spectricarus/EGL314_TeamF/Final/Software/assets/backgrounds/#1.png

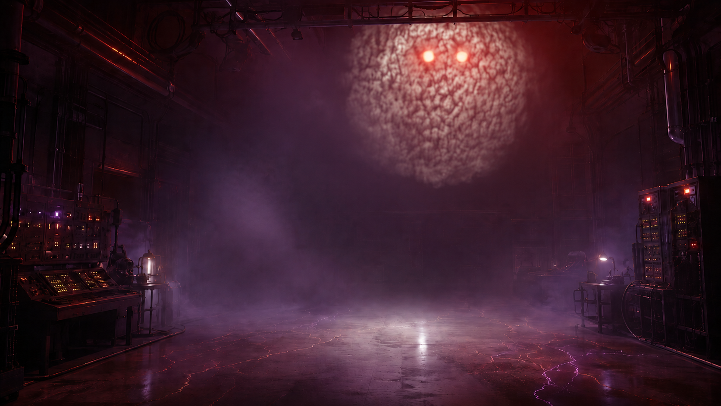
Final/Software/assets/backgrounds/#1.png
