spectricarus/EGL314_TeamF/Final/Software/assets/backgrounds/#3.png

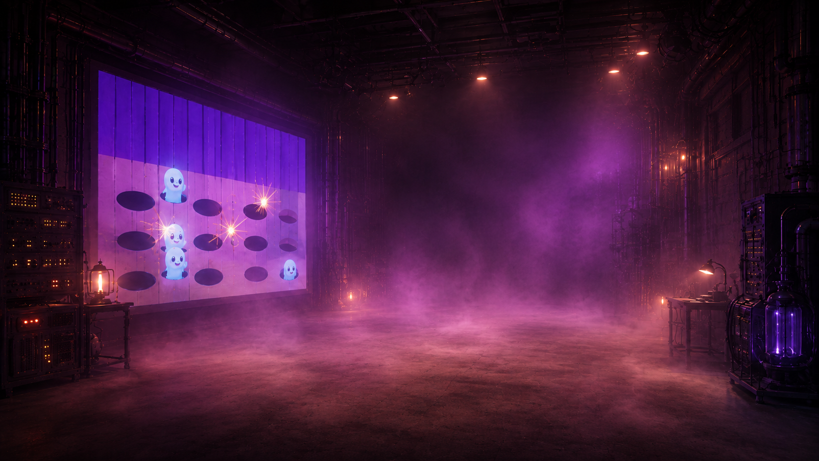
Final/Software/assets/backgrounds/#3.png
