spectricarus/EGL314_TeamF/Final/Software/assets/backgrounds/#5.png

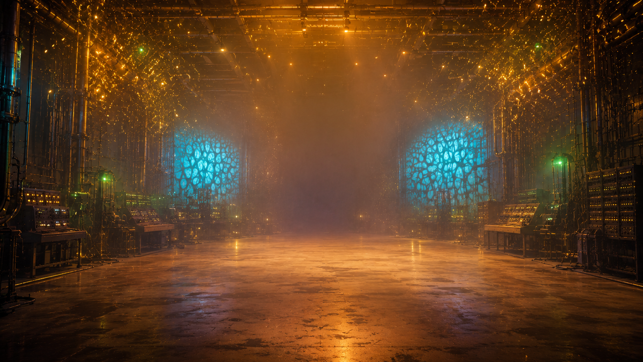
Final/Software/assets/backgrounds/#5.png
