spectricarus/EGL314_TeamF/MVP/Software/assets/pipeline-diagram.png

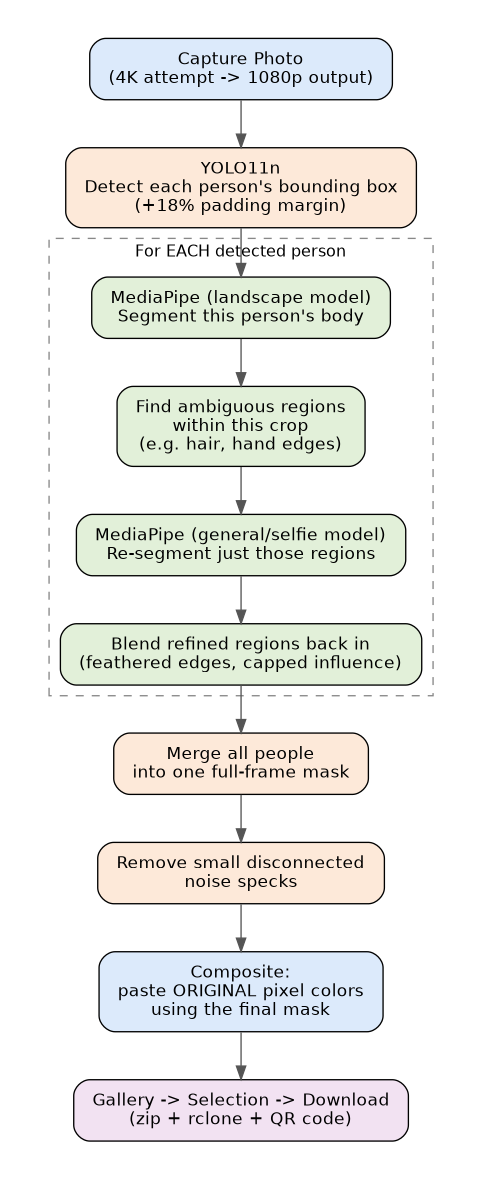
MVP/Software/assets/pipeline-diagram.png
