spectricarus/EGL314_TeamF/POC/images/power_touchcreen_via_pi.jpg

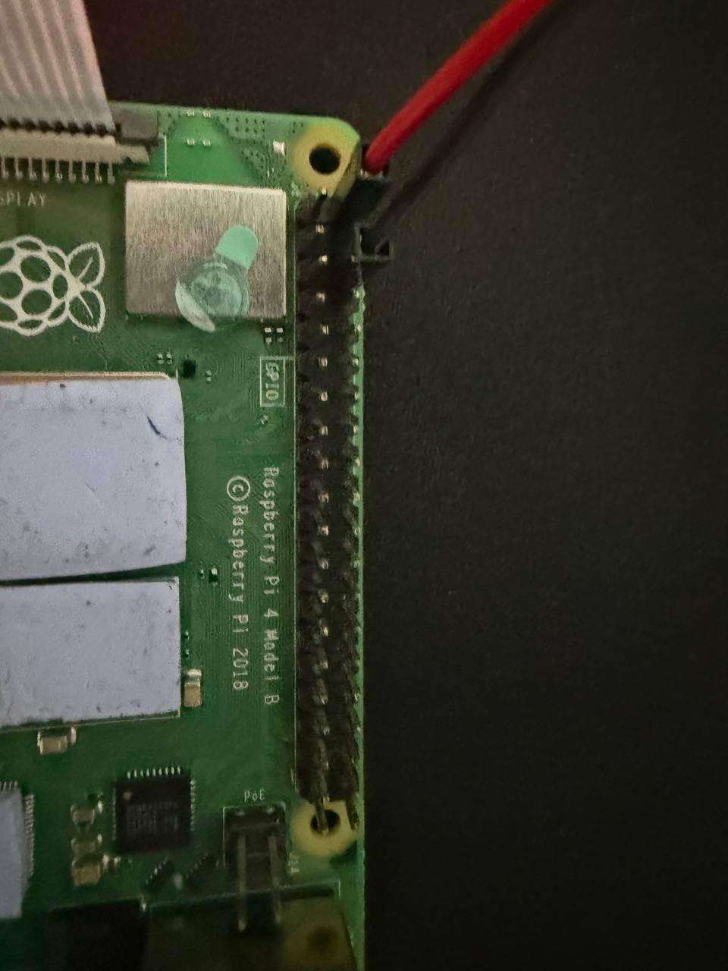
POC/images/power_touchcreen_via_pi.jpg
