spectricarus/EGL314_TeamF/POC/images/ribbon_connection.jpg

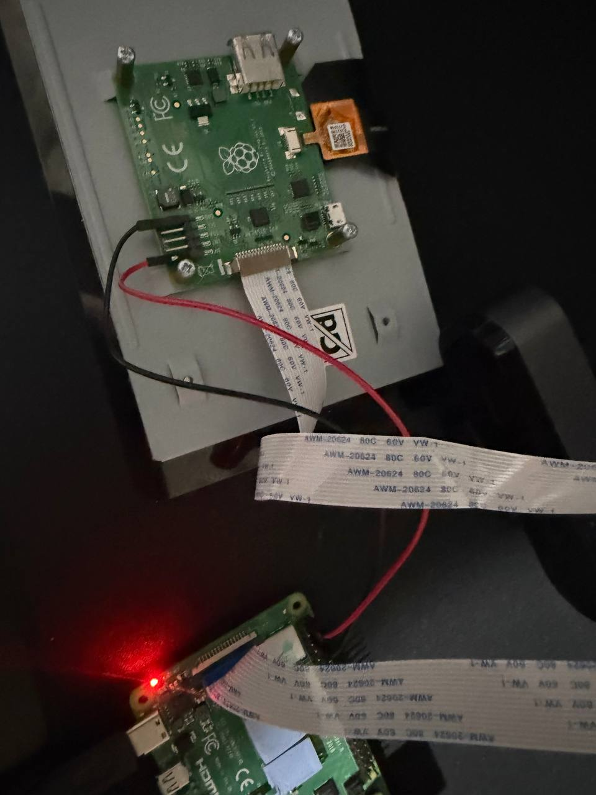
POC/images/ribbon_connection.jpg
