spectricarus/EGL314_TeamF/POC/Enclosure/POC/Images/assembly.jpg

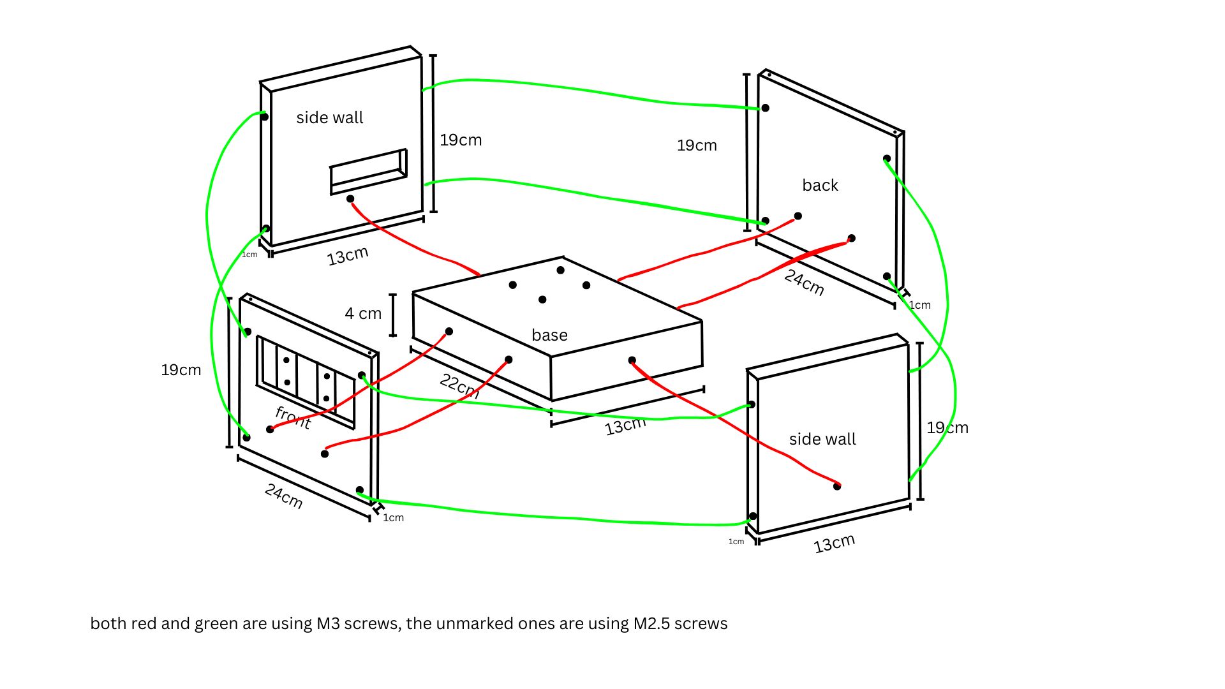
POC/Enclosure/POC/Images/assembly.jpg
