spectricarus/EGL314_TeamF/POC/Enclosure/POC/Images/base and front 3d print.jpg

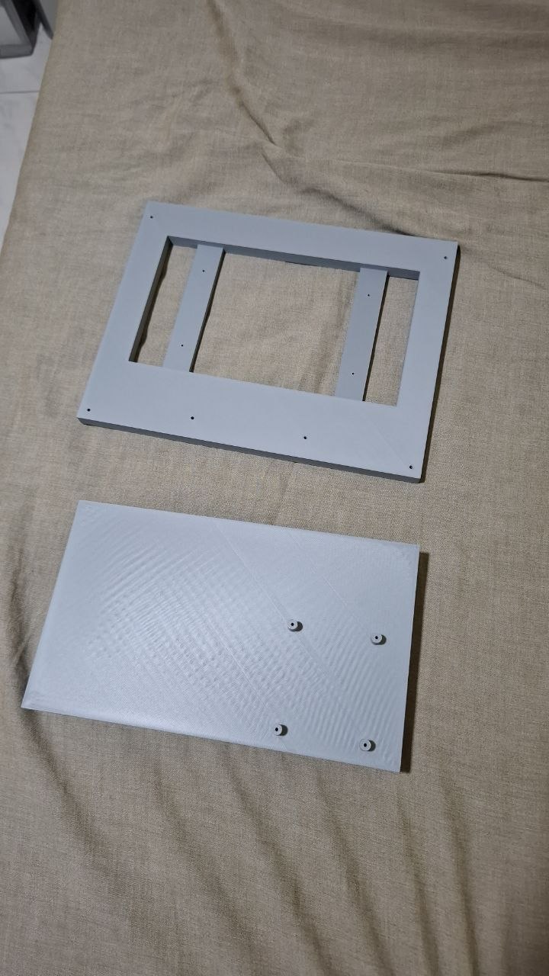
POC/Enclosure/POC/Images/base and front 3d print.jpg
